CycleStartProto/StargateBadge/graphics source files/atlantis stargate.jpg

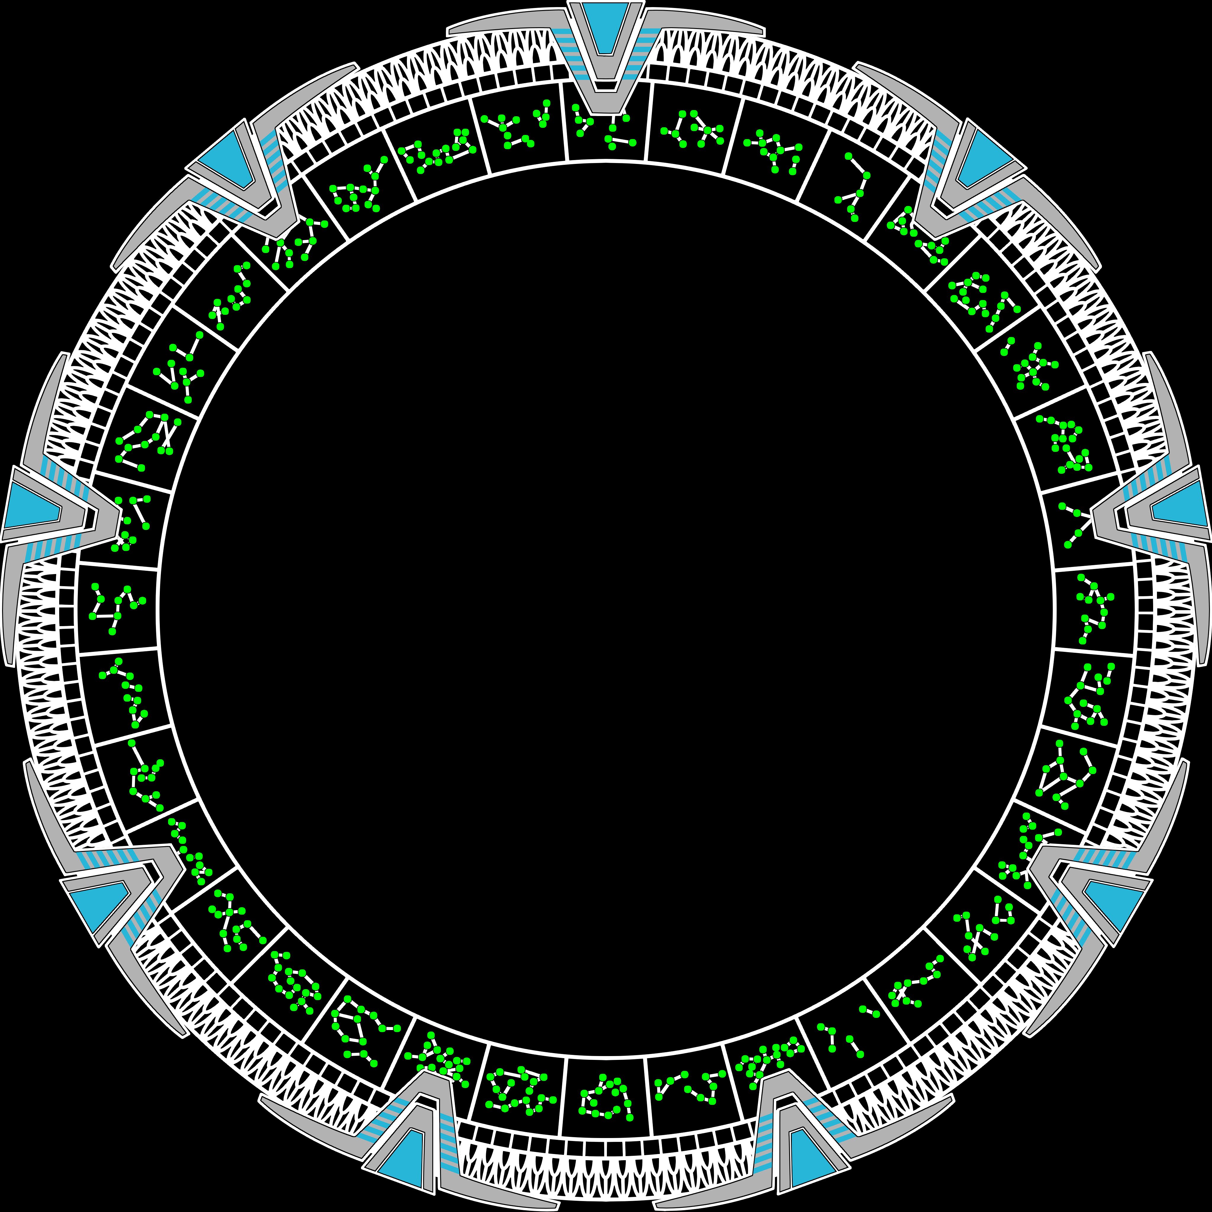
graphics source files/atlantis stargate.jpg
