CycleStartProto/StargateBadge/graphics source files/Github QR index.bmp

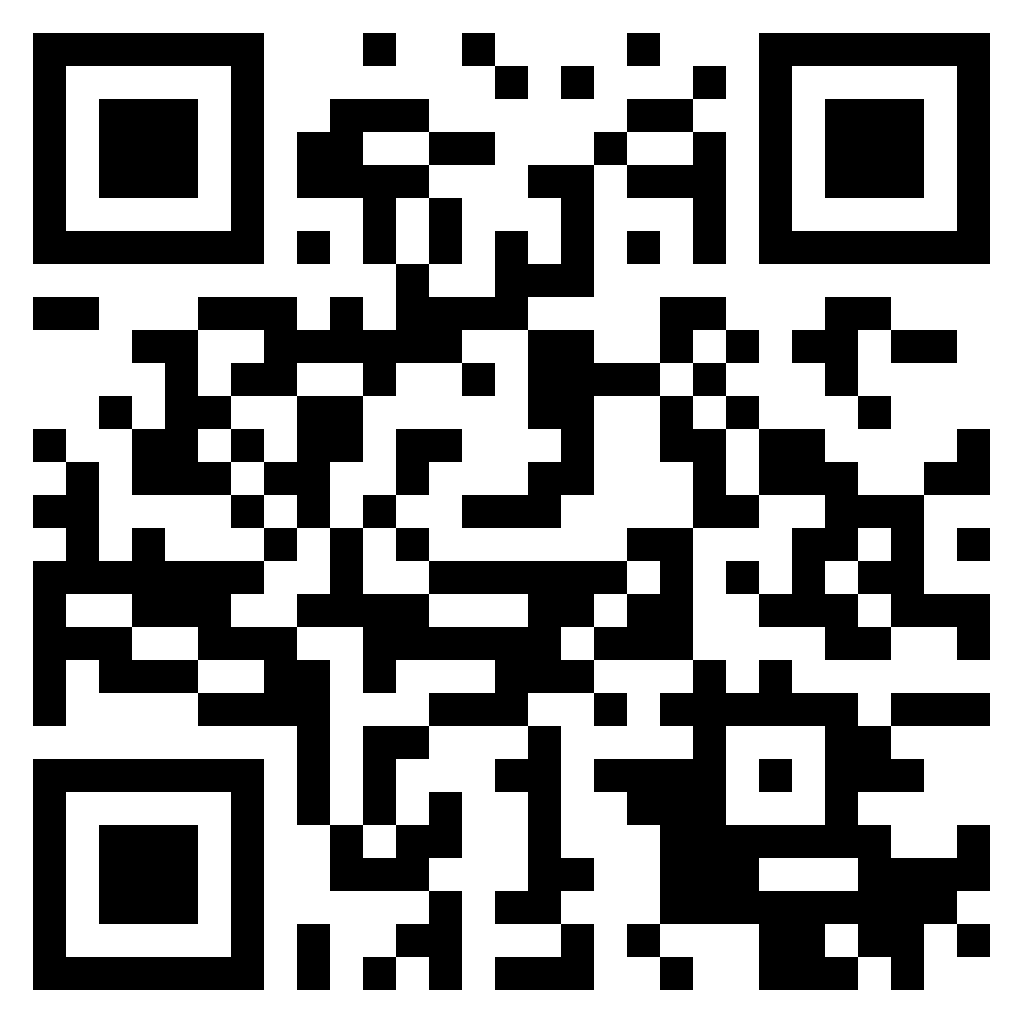
graphics source files/Github QR index.bmp
