CycleStartProto/StargateBadge/pictures/2024-06-16 22_03_29-Autodesk Fusion.png

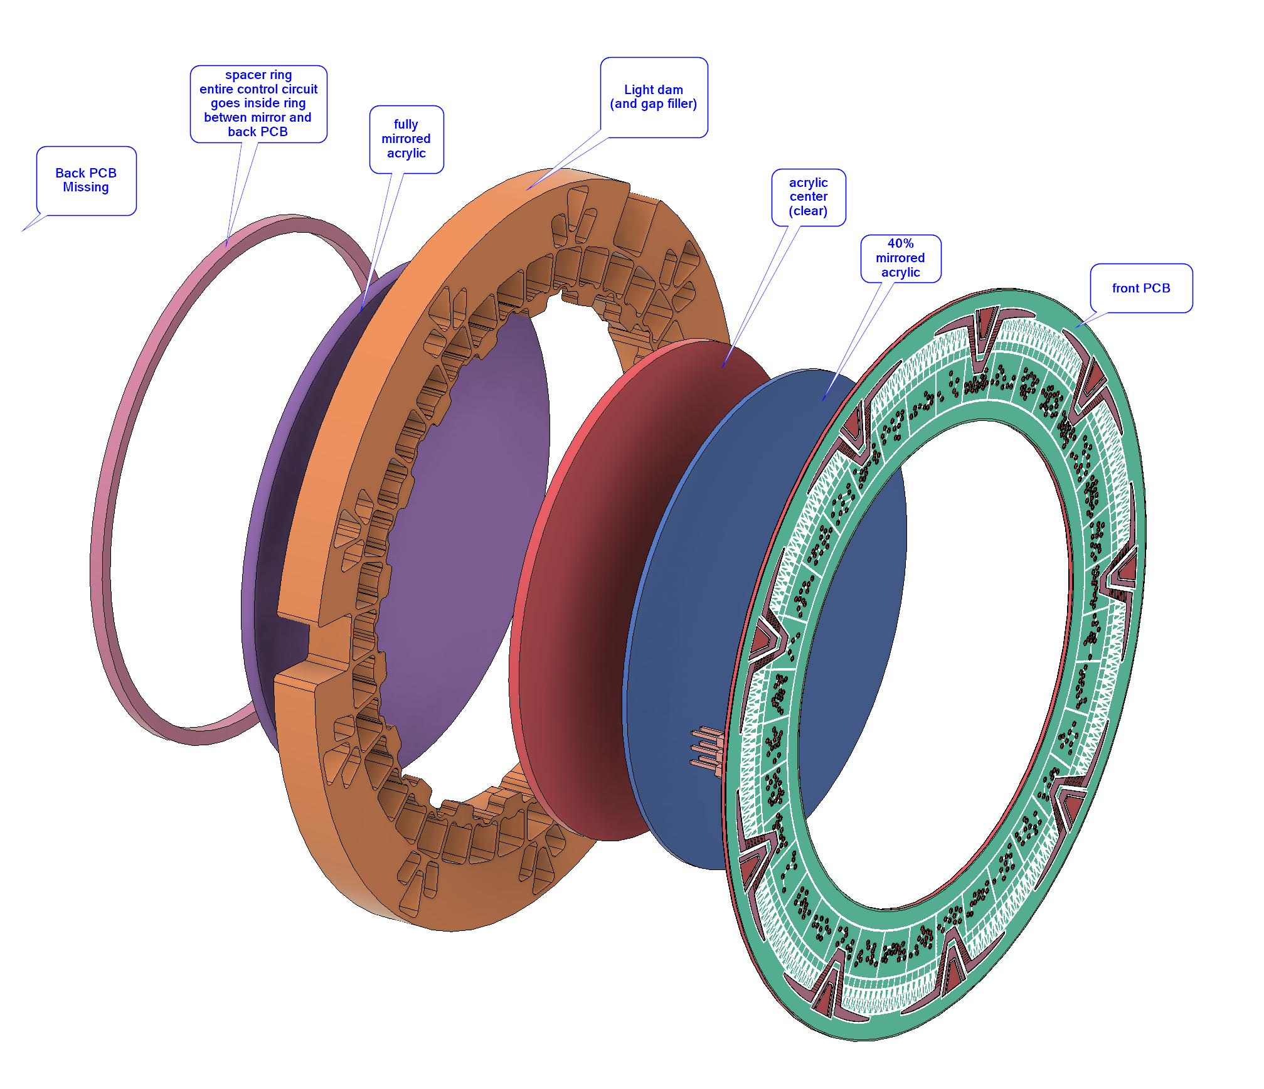
pictures/2024-06-16 22_03_29-Autodesk Fusion.png
