CycleStartProto/StargateBadge/pictures/70456e6e-29b1-4dbe-bf6e-9c9d87ef6c4b.PNG

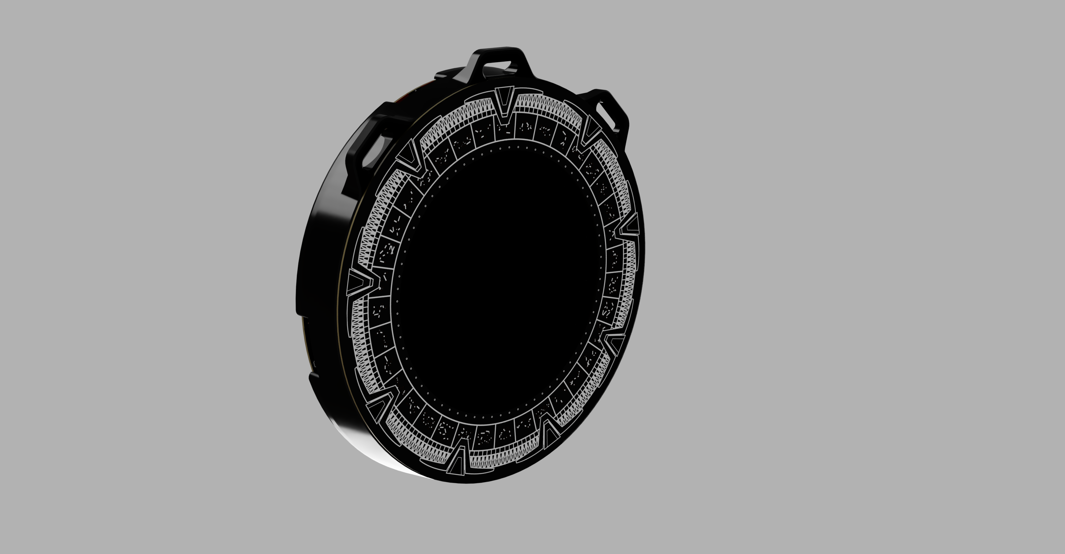
pictures/70456e6e-29b1-4dbe-bf6e-9c9d87ef6c4b.PNG
