CycleStartProto/StargateBadge/pictures/3290302A-Y25/1.jpg

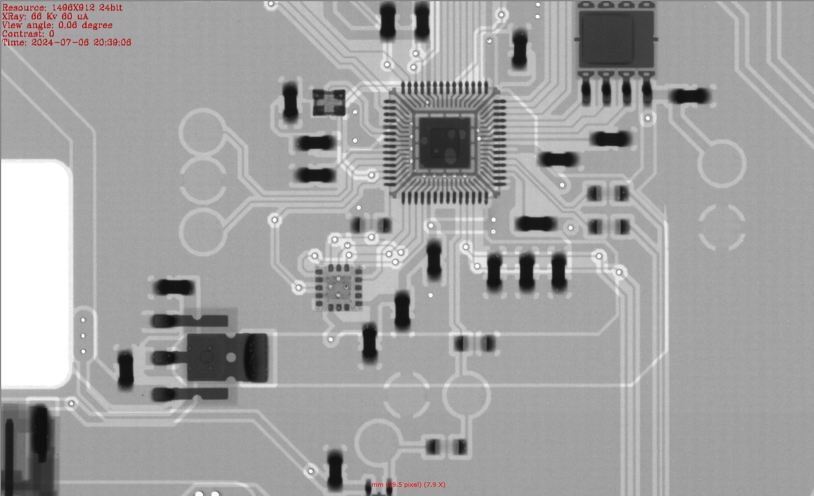
pictures/3290302A-Y25/1.jpg
