CycleStartProto/StargateBadge/pictures/3290302A-Y25/2.jpg

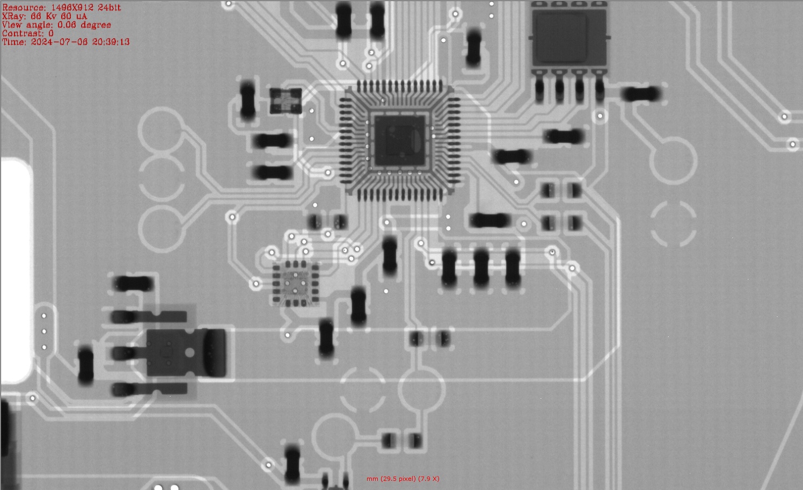
pictures/3290302A-Y25/2.jpg
