CycleStartProto/StargateBadge/pictures/3290302A-Y25/3.jpg

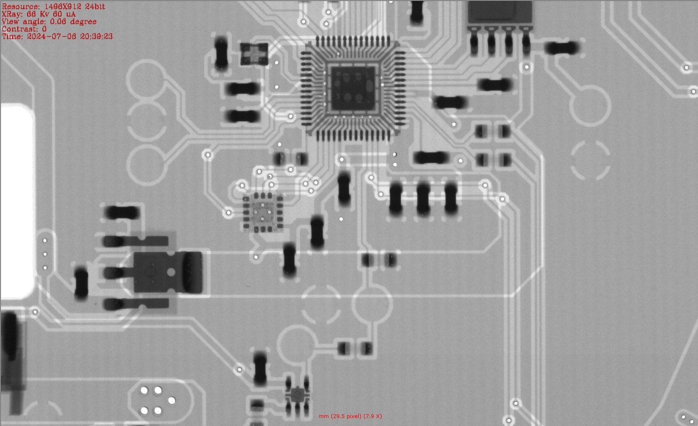
pictures/3290302A-Y25/3.jpg
