CycleStartProto/StargateBadge/pictures/3290302A-Y25/4.jpg

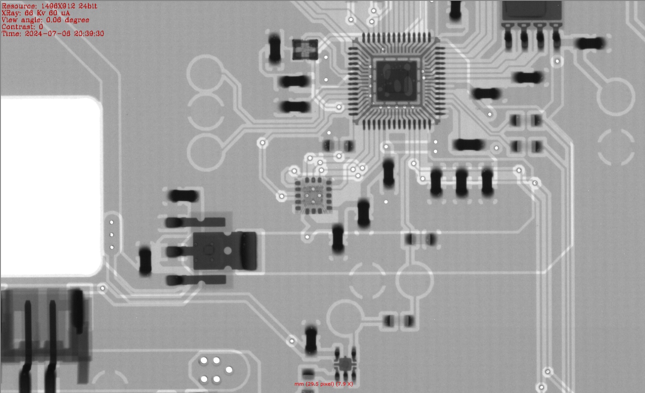
pictures/3290302A-Y25/4.jpg
