CycleStartProto/StargateBadge/pictures/3290302A-Y25/5.jpg

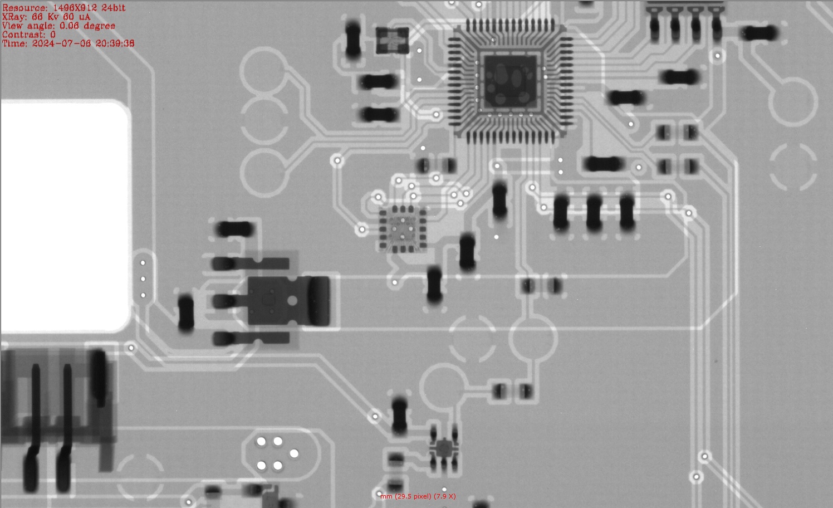
pictures/3290302A-Y25/5.jpg
