CycleStartProto/StargateBadge/hardware/circuit boards/front board/Front_Board_v6.sch

## EAGLE design hardware/circuit boards/front board/Front_Board_v6.sch (2024-07-19)

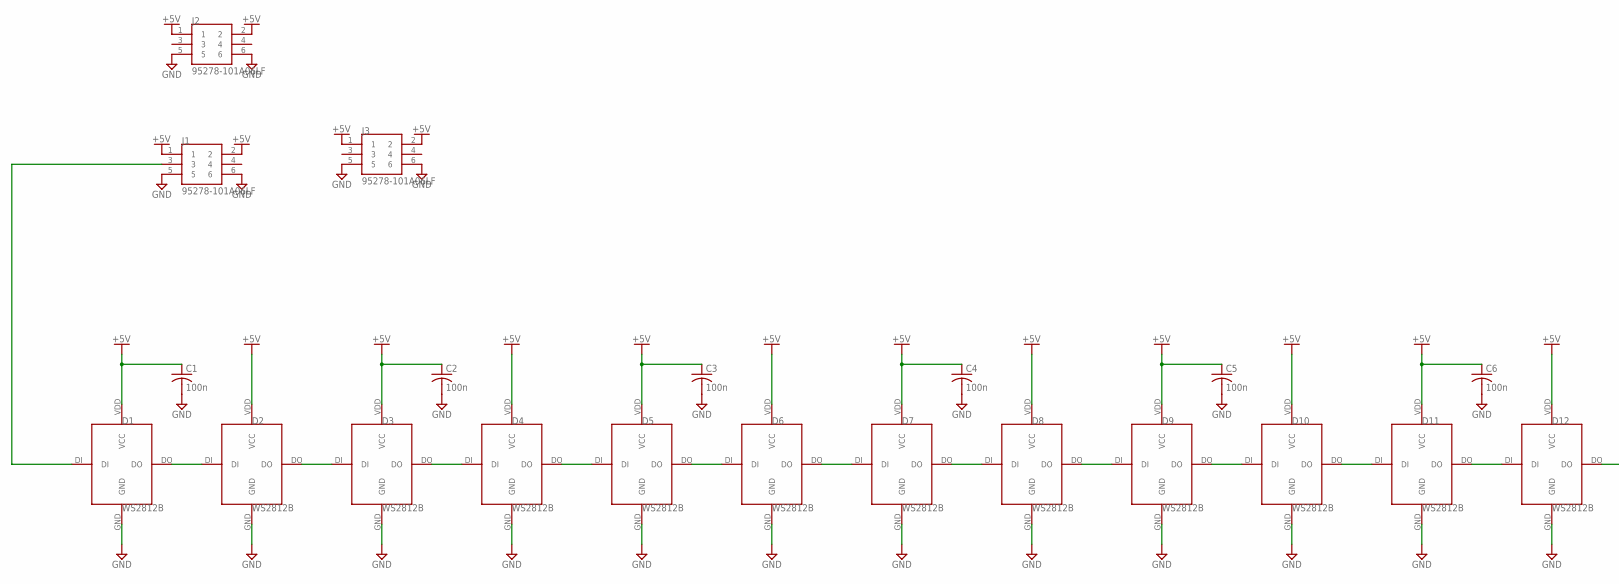
[picture p20: schematic Front_Board_v6.sch, part in row 1, column 1]

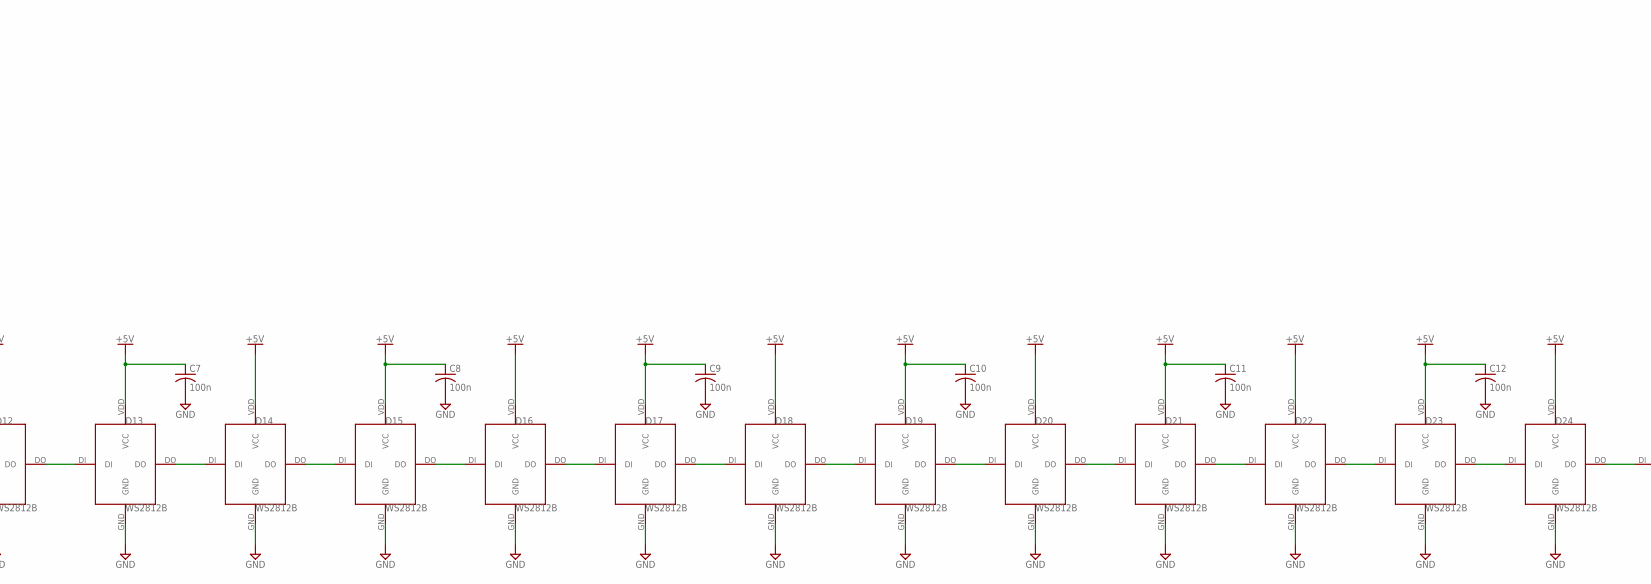
[picture p21: schematic Front_Board_v6.sch, part in row 1, column 2]

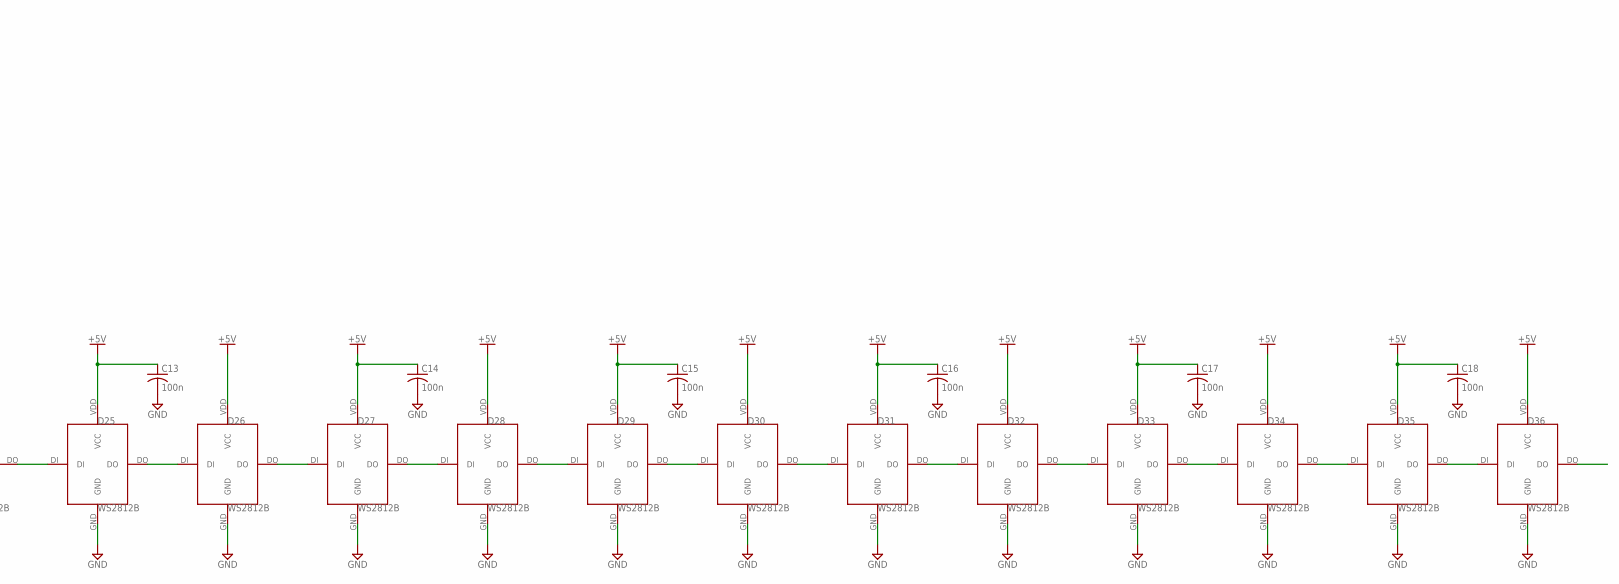
[picture p22: schematic Front_Board_v6.sch, part in row 1, column 3]

Parts:
C1, C2, C3, C4, C5, C6, C7, C8, C9, C10, C11, C12, C13, C14, C15, C16, C17, C18: 100n; C0603K
D1, D2, D3, D4, D5, D6, D7, D8, D9, D10, D11, D12, D13, D14, D15, D16, D17, D18, D19, D20, D21, D22, D23, D24, D25, D26, D27, D28, D29, D30, D31, D32, D33, D34, D35, D36: WS2812B; 1010
J1, J2, J3: 95278-101A06LF

Connections:
+5V: C1.1, C2.1, C3.1, C4.1, C5.1, C6.1, C7.1, C8.1, C9.1, C10.1, C11.1, C12.1, C13.1, C14.1, C15.1, C16.1, C17.1, C18.1, D1.VDD (VCC), D2.VDD (VCC), D3.VDD (VCC), D4.VDD (VCC), D5.VDD (VCC), D6.VDD (VCC), D7.VDD (VCC), D8.VDD (VCC), D9.VDD (VCC), D10.VDD (VCC), D11.VDD (VCC), D12.VDD (VCC), D13.VDD (VCC), D14.VDD (VCC), D15.VDD (VCC), D16.VDD (VCC), D17.VDD (VCC), D18.VDD (VCC), D19.VDD (VCC), D20.VDD (VCC), D21.VDD (VCC), D22.VDD (VCC), D23.VDD (VCC), D24.VDD (VCC), D25.VDD (VCC), D26.VDD (VCC), D27.VDD (VCC), D28.VDD (VCC), D29.VDD (VCC), D30.VDD (VCC), D31.VDD (VCC), D32.VDD (VCC), D33.VDD (VCC), D34.VDD (VCC), D35.VDD (VCC), D36.VDD (VCC), J1.1, J1.2, J2.1, J2.2, J3.1, J3.2
GND: C1.2, C2.2, C3.2, C4.2, C5.2, C6.2, C7.2, C8.2, C9.2, C10.2, C11.2, C12.2, C13.2, C14.2, C15.2, C16.2, C17.2, C18.2, D1.GND, D2.GND, D3.GND, D4.GND, D5.GND, D6.GND, D7.GND, D8.GND, D9.GND, D10.GND, D11.GND, D12.GND, D13.GND, D14.GND, D15.GND, D16.GND, D17.GND, D18.GND, D19.GND, D20.GND, D21.GND, D22.GND, D23.GND, D24.GND, D25.GND, D26.GND, D27.GND, D28.GND, D29.GND, D30.GND, D31.GND, D32.GND, D33.GND, D34.GND, D35.GND, D36.GND, J1.5, J1.6, J2.5, J2.6, J3.5, J3.6
unnamed: D1.DO, D2.DI
unnamed: D2.DO, D3.DI
unnamed: D3.DO, D4.DI
unnamed: D4.DO, D5.DI
unnamed: D5.DO, D6.DI
unnamed: D6.DO, D7.DI
unnamed: D7.DO, D8.DI
unnamed: D8.DO, D9.DI
unnamed: D9.DO, D10.DI
unnamed: D10.DO, D11.DI
unnamed: D11.DO, D12.DI
unnamed: D12.DO, D13.DI
unnamed: D13.DO, D14.DI
unnamed: D14.DO, D15.DI
unnamed: D15.DO, D16.DI
unnamed: D16.DO, D17.DI
unnamed: D17.DO, D18.DI
unnamed: D18.DO, D19.DI
unnamed: D19.DO, D20.DI
unnamed: D20.DO, D21.DI
unnamed: D21.DO, D22.DI
unnamed: D22.DO, D23.DI
unnamed: D23.DO, D24.DI
unnamed: D24.DO, D25.DI
unnamed: D25.DO, D26.DI
unnamed: D26.DO, D27.DI
unnamed: D27.DO, D28.DI
unnamed: D28.DO, D29.DI
unnamed: D29.DO, D30.DI
unnamed: D30.DO, D31.DI
unnamed: D31.DO, D32.DI
unnamed: D32.DO, D33.DI
unnamed: D1.DI, J1.3
unnamed: D33.DO, D34.DI
unnamed: D34.DO, D35.DI
unnamed: D35.DO, D36.DI
